user-jackie/Smart-Refrigerator/5.PCB File(made by jlc)/assets/image-20260305090433791.png

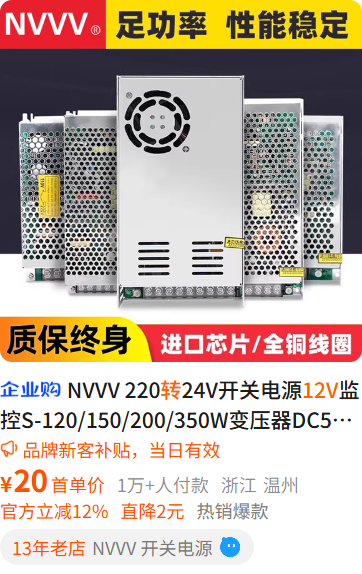
5.PCB File(made by jlc)/assets/image-20260305090433791.png
