user-jackie/Smart-Refrigerator/5.PCB File(made by jlc)/assets/image-20260305092447857.png

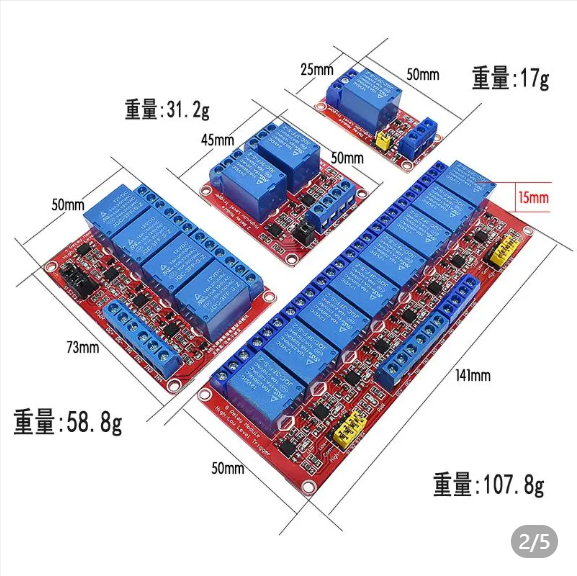
5.PCB File(made by jlc)/assets/image-20260305092447857.png
