user-jackie/Smart-Refrigerator/1.Shell(made by SW)/冰箱零件和装配体/继电器装配体.SLDASM

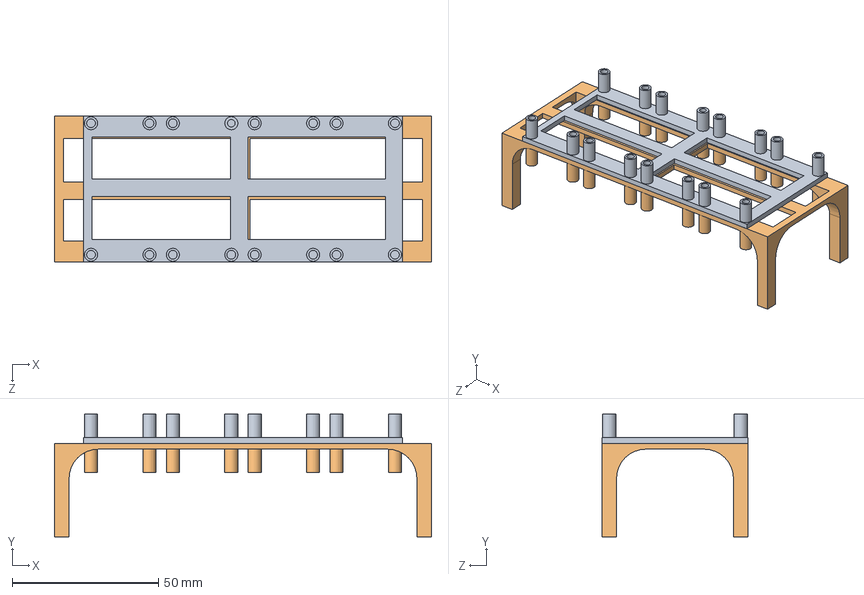
[picture p23: CAD file, 2026-03-05]
1.Shell(made by SW)/冰箱零件和装配体/继电器装配体.SLDASM
129.0 x 42.0 x 50.0 mm
继电器壳2
继电器壳
