user-jackie/Smart-Refrigerator/1.Shell(made by SW)/冰箱零件和装配体/装配体.SLDASM

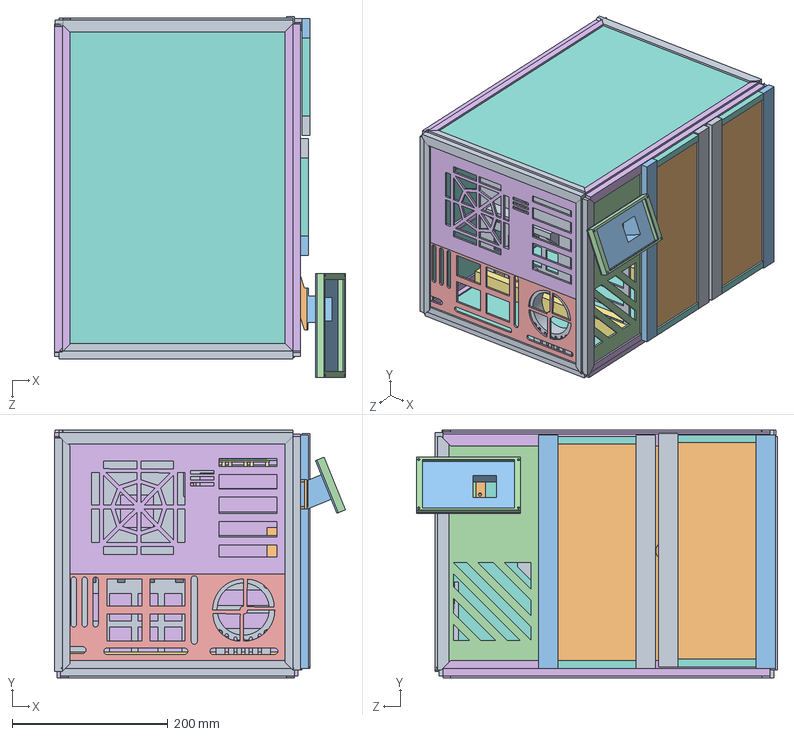
[picture p24: CAD file, 2026-03-05]
1.Shell(made by SW)/冰箱零件和装配体/装配体.SLDASM
373.7 x 318.0 x 464.2 mm
冰箱顶连接-短边 x 8
冰箱顶 x 3
冰箱侧1
冰箱顶连接-长边 x 4
冰箱侧2下
冰箱电源门
冰箱门 x 2
冰箱门亚克力 x 2
冰箱门磁吸侧 x 2
冰箱门包围 x 4
内胆卡槽 x 4
冰箱内冷热隔板
内胆顶 x 2
内胆热侧
内胆冷侧
内胆门吸
冰箱内电源隔板
继电器壳2
继电器壳
冰箱侧2上
PCB支撑
前屏幕罩
后屏幕罩
屏幕连接
空气净化外壳
