user-jackie/Smart-Refrigerator/1.Shell(made by SW)/冰箱零件和装配体/电源隔板装配体.SLDASM

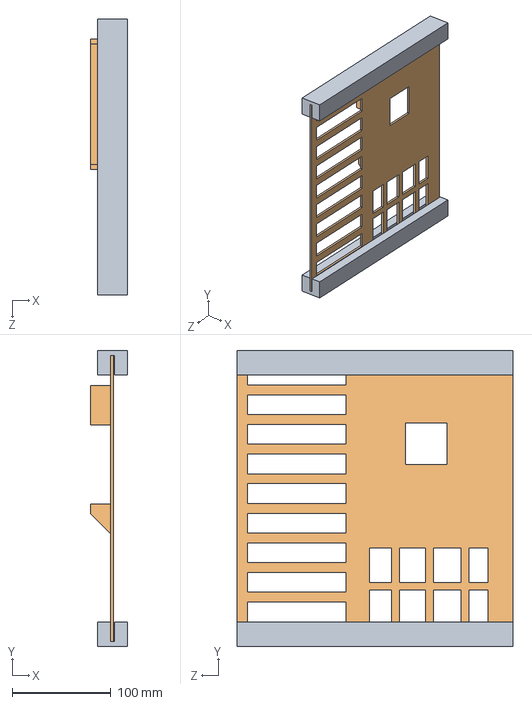
[picture p25: CAD file, 2026-03-05]
1.Shell(made by SW)/冰箱零件和装配体/电源隔板装配体.SLDASM
37.0 x 300.0 x 280.0 mm
冰箱内电源隔板
内胆卡槽 x 2
