user-jackie/Smart-Refrigerator/1.Shell(made by SW)/冰箱零件和装配体/屏幕装配体.SLDASM

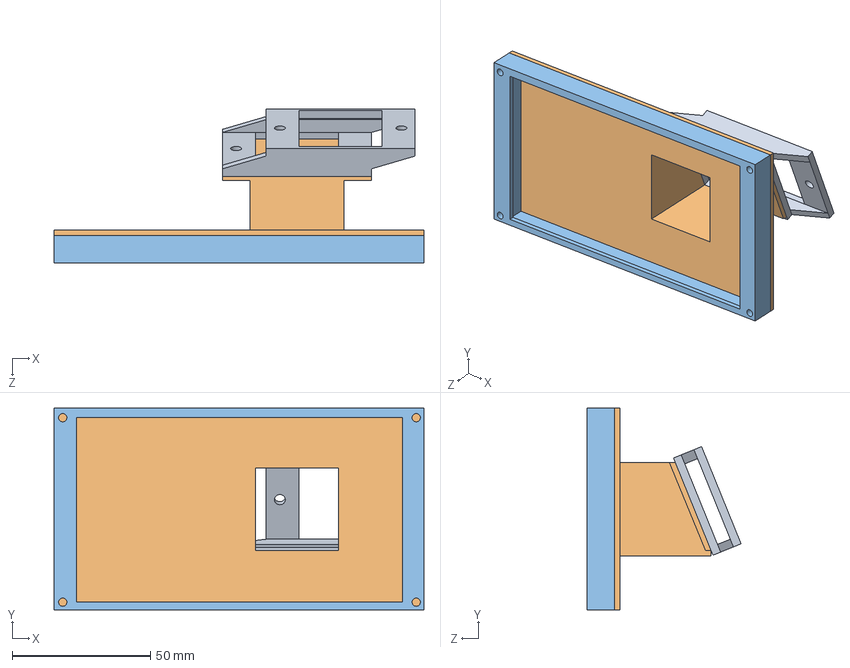
[picture p26: CAD file, 2026-03-05]
1.Shell(made by SW)/冰箱零件和装配体/屏幕装配体.SLDASM
134.0 x 73.0 x 55.9 mm
前屏幕罩
后屏幕罩
屏幕连接
