user-jackie/Smart-Refrigerator/1.Shell(made by SW)/打印文件/继电器壳2.STL

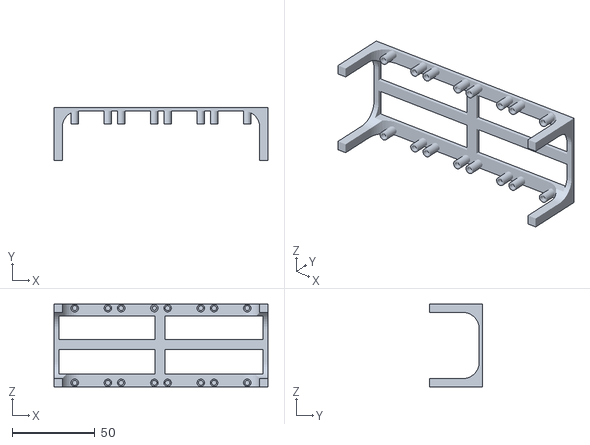
[picture p39: CAD file, 2026-03-05]
1.Shell(made by SW)/打印文件/继电器壳2.STL
129.0 x 32.0 x 50.0
