user-jackie/Smart-Refrigerator/1.Shell(made by SW)/冰箱零件和装配体/六角螺栓 M6x5.SLDPRT

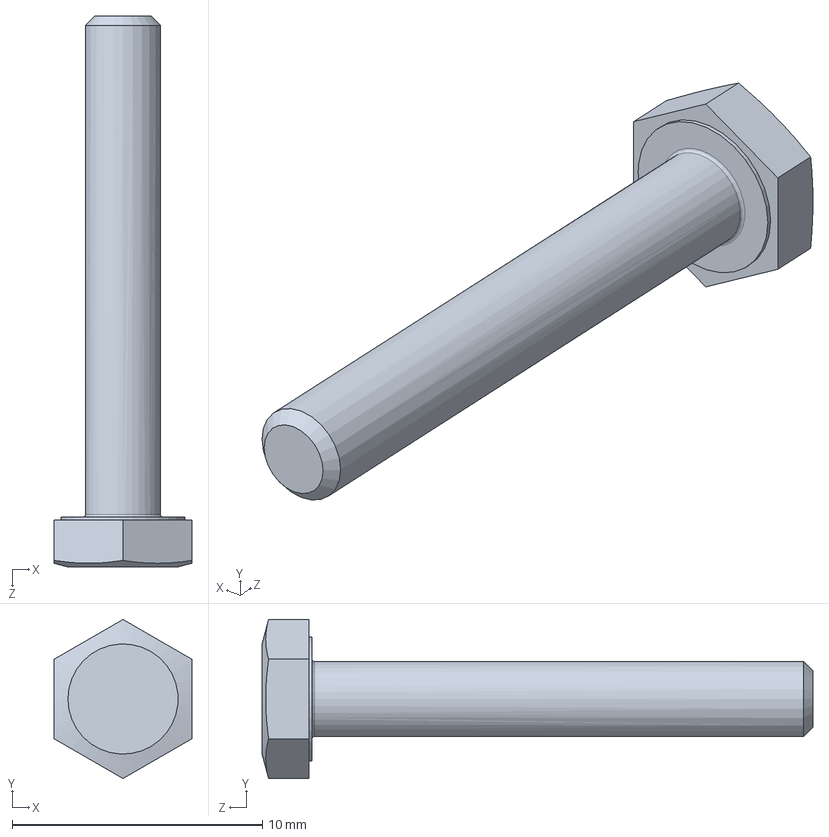
[picture p40: CAD file, 2026-03-05]
1.Shell(made by SW)/冰箱零件和装配体/六角螺栓 M6x5.SLDPRT
5.50 x 6.35 x 22.0 mm
