user-jackie/Smart-Refrigerator/1.Shell(made by SW)/打印文件/内胆热侧001.stl

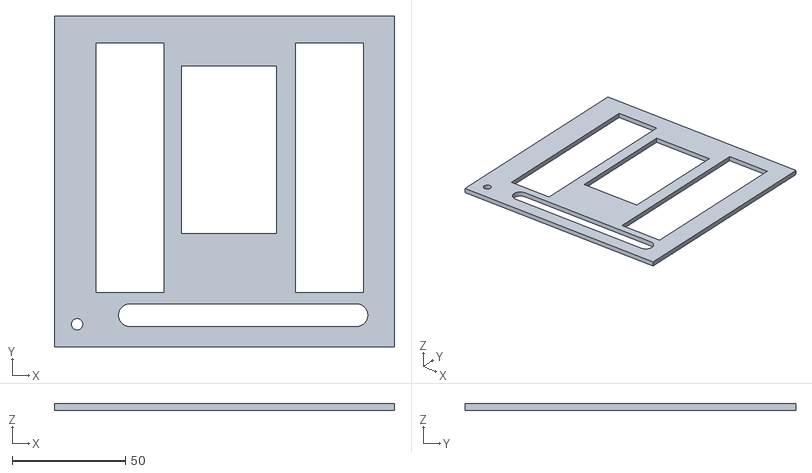
[picture p41: CAD file, 2026-03-05]
1.Shell(made by SW)/打印文件/内胆热侧001.stl
150.0 x 145.9 x 3.00
