user-jackie/Smart-Refrigerator/1.Shell(made by SW)/打印文件/冰箱门包围.STL

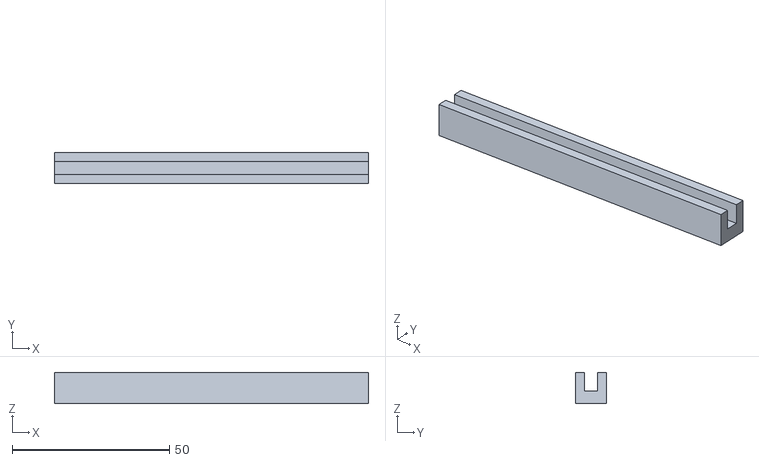
[picture p42: CAD file, 2026-03-05]
1.Shell(made by SW)/打印文件/冰箱门包围.STL
100.0 x 10.0 x 10.0
