user-jackie/Smart-Refrigerator/1.Shell(made by SW)/冰箱零件和装配体/冰箱门连接.SLDPRT

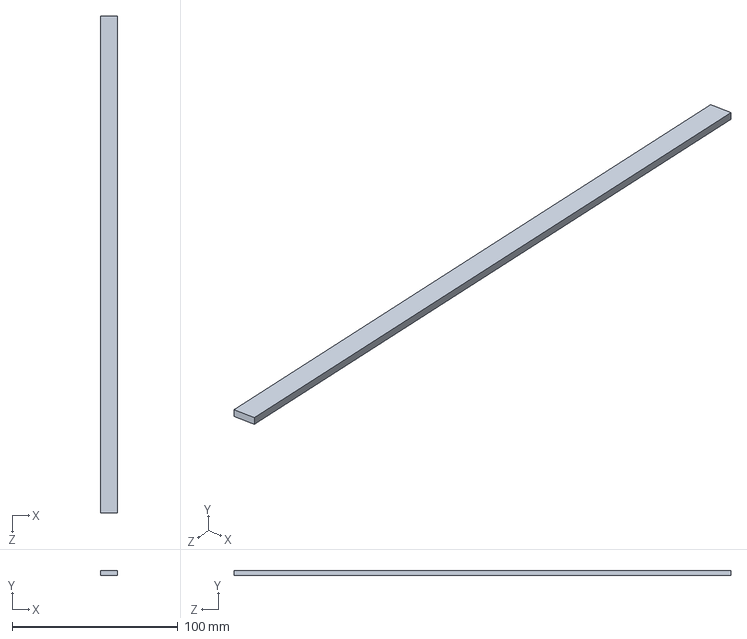
[picture p43: CAD file, 2026-03-05]
1.Shell(made by SW)/冰箱零件和装配体/冰箱门连接.SLDPRT
10.0 x 3.00 x 300.0 mm
