user-jackie/Smart-Refrigerator/1.Shell(made by SW)/打印文件/前屏幕罩.STL

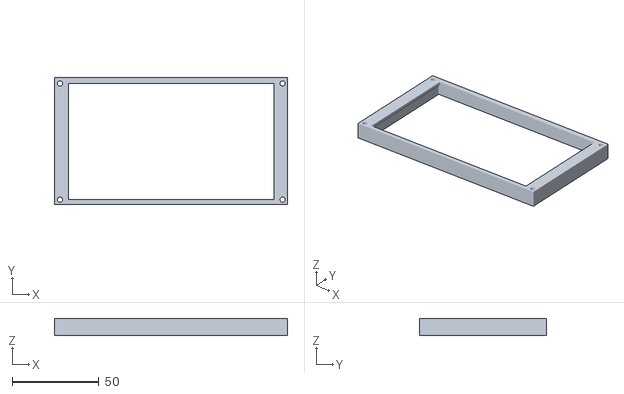
[picture p44: CAD file, 2026-03-05]
1.Shell(made by SW)/打印文件/前屏幕罩.STL
134.0 x 73.0 x 10.0
