user-jackie/Smart-Refrigerator/1.Shell(made by SW)/冰箱零件和装配体/冰箱.SLDPRT

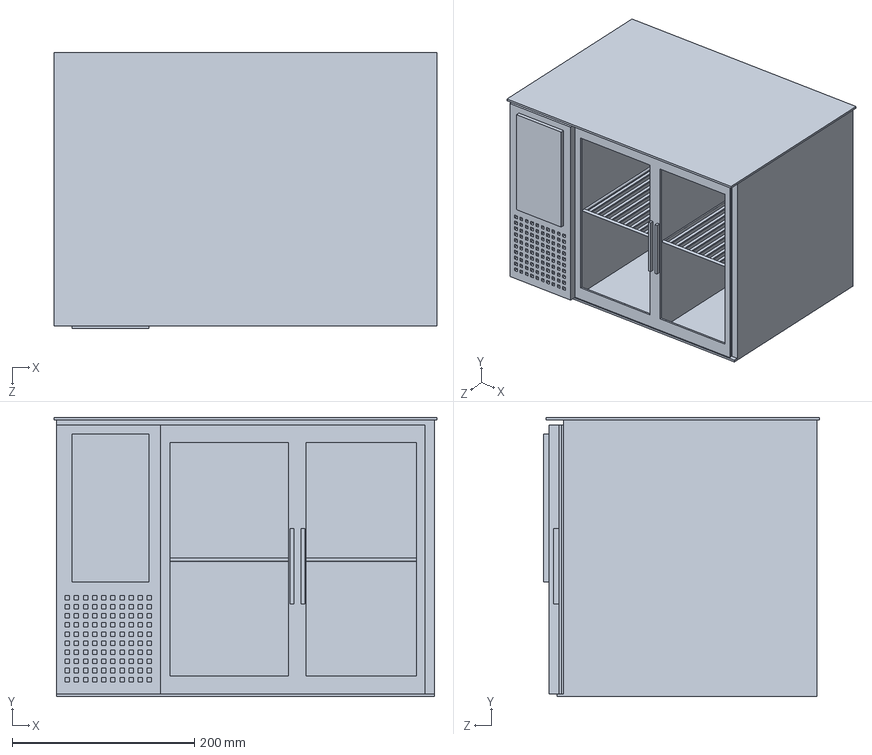
[picture p45: CAD file, 2026-03-05]
1.Shell(made by SW)/冰箱零件和装配体/冰箱.SLDPRT
420.0 x 306.0 x 303.0 mm
