user-jackie/Smart-Refrigerator/1.Shell(made by SW)/打印文件/冰箱电源门001.stl

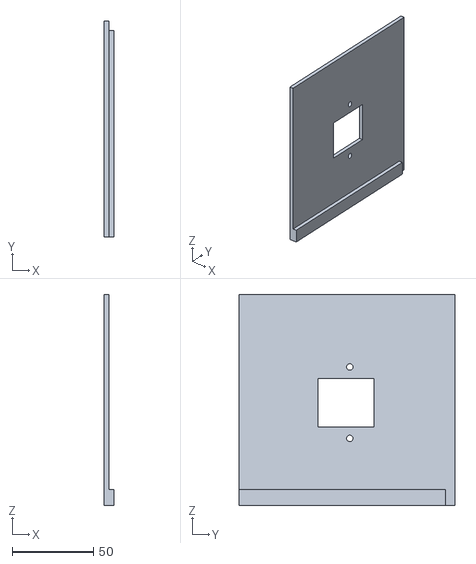
[picture p46: CAD file, 2026-03-05]
1.Shell(made by SW)/打印文件/冰箱电源门001.stl
6.00 x 133.1 x 130.0
