user-jackie/Smart-Refrigerator/1.Shell(made by SW)/打印文件/空气净化外壳.STL

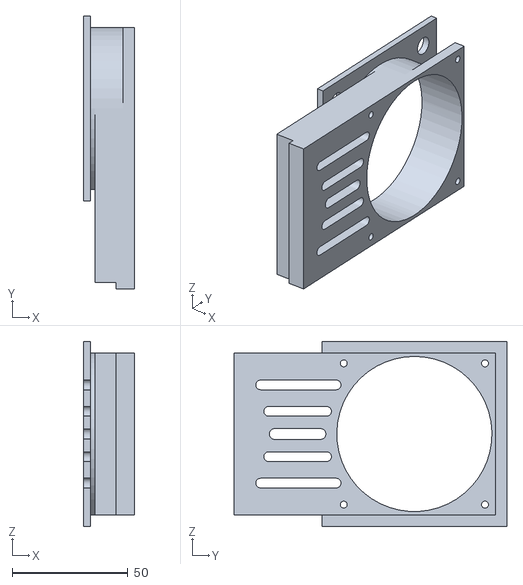
[picture p48: CAD file, 2026-03-05]
1.Shell(made by SW)/打印文件/空气净化外壳.STL
22.0 x 117.9 x 80.0
