user-jackie/Smart-Refrigerator/1.Shell(made by SW)/冰箱零件和装配体/侧连接.SLDPRT

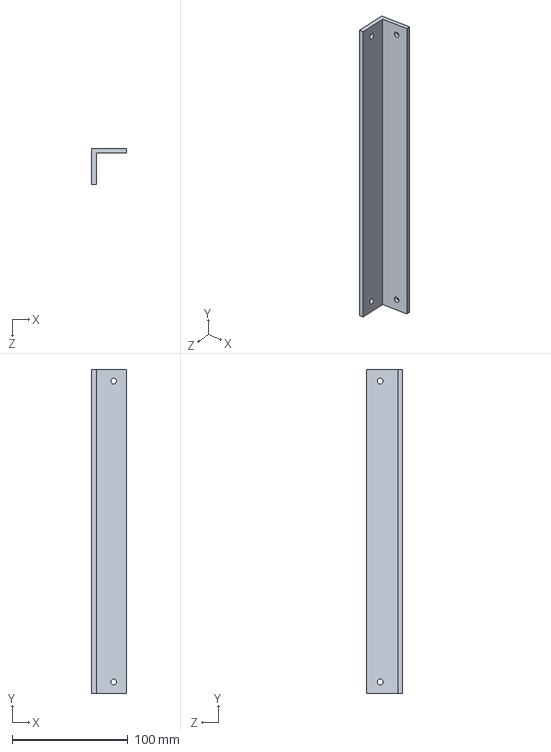
[picture p49: CAD file, 2026-03-05]
1.Shell(made by SW)/冰箱零件和装配体/侧连接.SLDPRT
30.0 x 280.0 x 30.7 mm
