user-jackie/Smart-Refrigerator/1.Shell(made by SW)/打印文件/冰箱内电源隔板004.stl

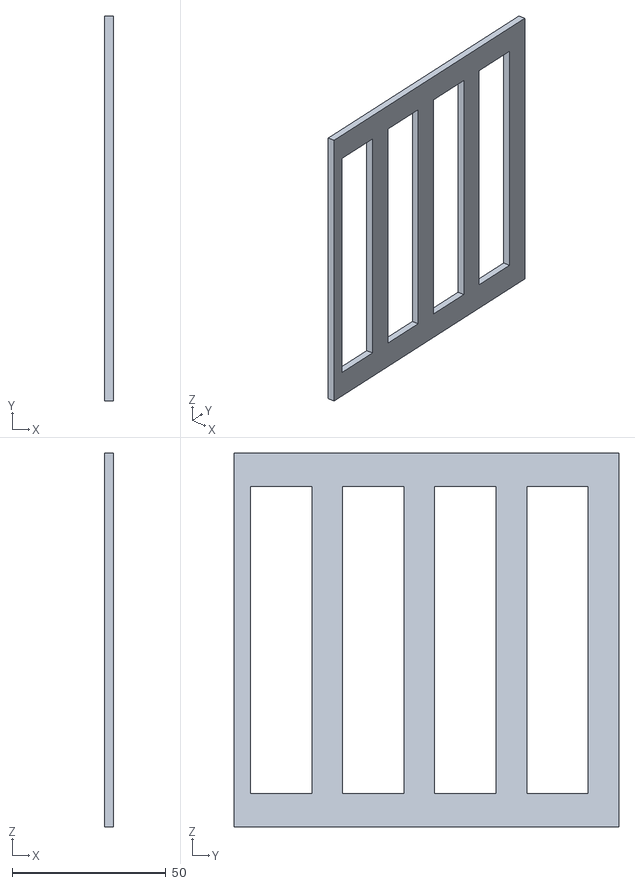
[picture p50: CAD file, 2026-03-05]
1.Shell(made by SW)/打印文件/冰箱内电源隔板004.stl
3.00 x 125.3 x 121.8
