user-jackie/Smart-Refrigerator/1.Shell(made by SW)/打印文件/冰箱侧2下.STL

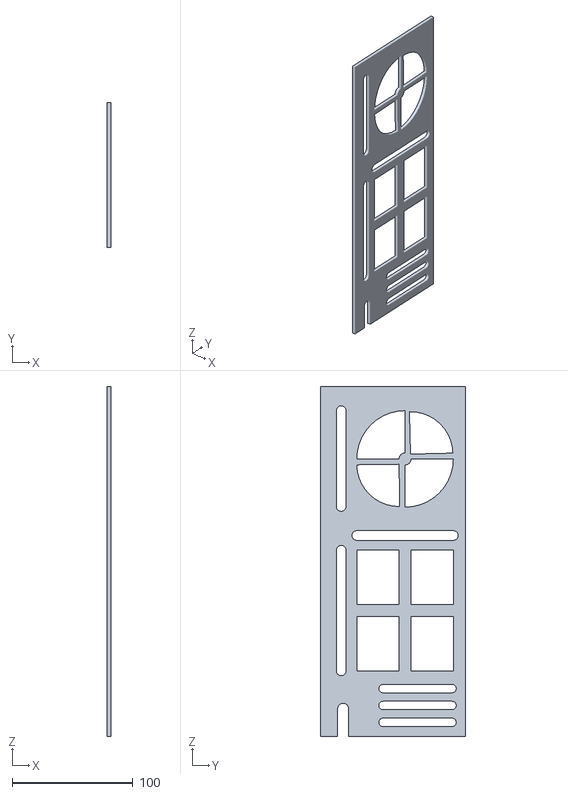
[picture p51: CAD file, 2026-03-05]
1.Shell(made by SW)/打印文件/冰箱侧2下.STL
3.00 x 120.0 x 290.0
