user-jackie/Smart-Refrigerator/1.Shell(made by SW)/打印文件/内胆卡槽.STL

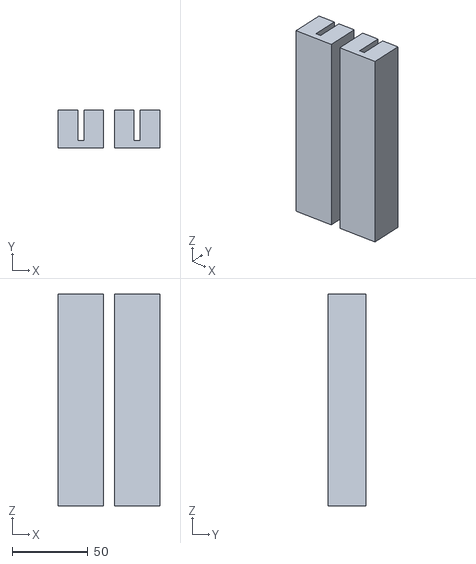
[picture p53: CAD file, 2026-03-05]
1.Shell(made by SW)/打印文件/内胆卡槽.STL
67.3 x 25.0 x 140.0
