user-jackie/Smart-Refrigerator/1.Shell(made by SW)/打印文件/内胆冷侧002.stl

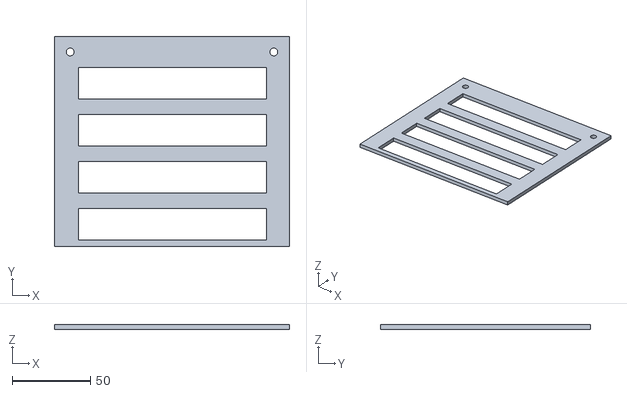
[picture p54: CAD file, 2026-03-05]
1.Shell(made by SW)/打印文件/内胆冷侧002.stl
150.0 x 134.3 x 3.00
