user-jackie/Smart-Refrigerator/1.Shell(made by SW)/冰箱零件和装配体/冰箱门.SLDPRT

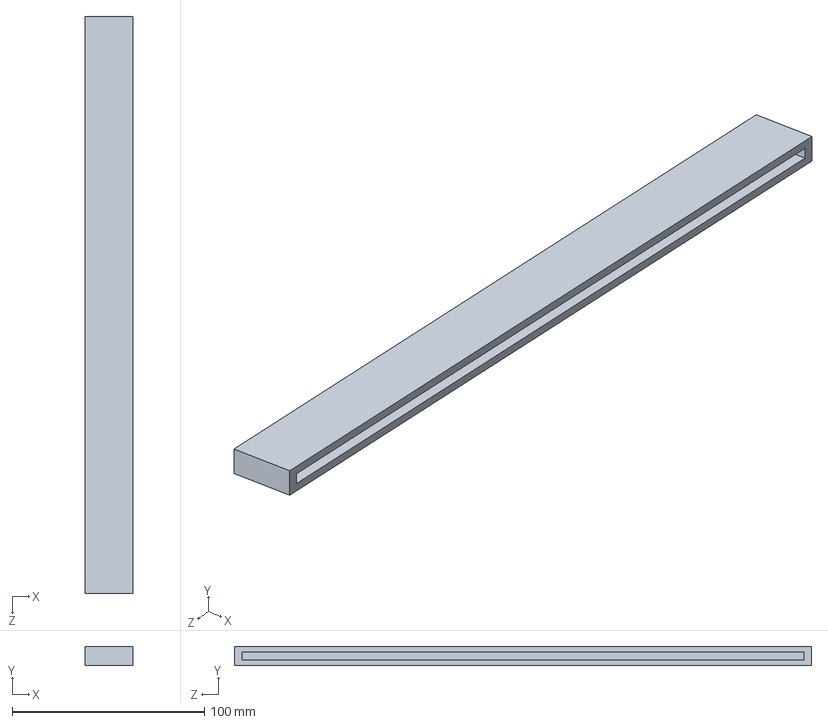
[picture p55: CAD file, 2026-03-05]
1.Shell(made by SW)/冰箱零件和装配体/冰箱门.SLDPRT
25.0 x 10.0 x 300.0 mm
