user-jackie/Smart-Refrigerator/1.Shell(made by SW)/打印文件/冰箱顶连接-短边.stl

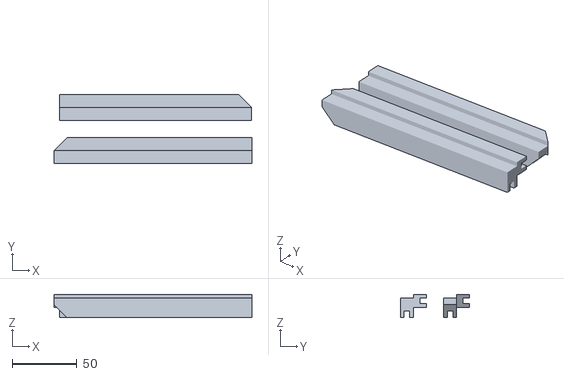
[picture p58: CAD file, 2026-03-05]
1.Shell(made by SW)/打印文件/冰箱顶连接-短边.stl
152.3 x 53.3 x 18.0
