user-jackie/Smart-Refrigerator/1.Shell(made by SW)/打印文件/冰箱内电源隔板001.stl

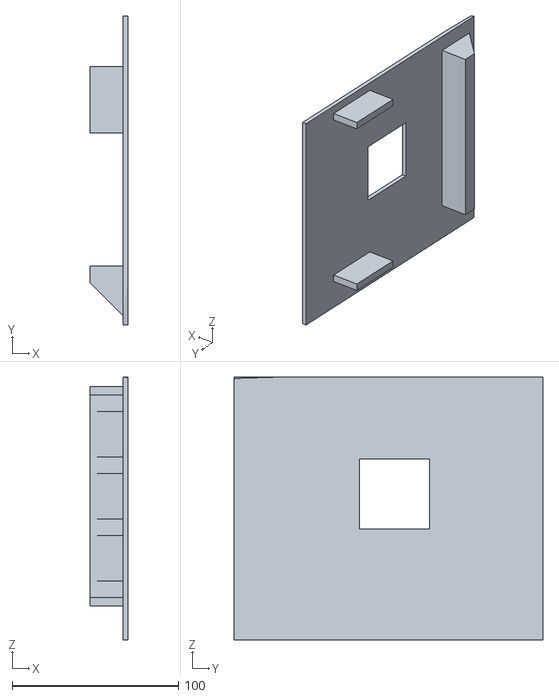
[picture p59: CAD file, 2026-03-05]
1.Shell(made by SW)/打印文件/冰箱内电源隔板001.stl
23.0 x 185.8 x 158.2
