user-jackie/Smart-Refrigerator/1.Shell(made by SW)/冰箱零件和装配体/PCB支撑.SLDPRT

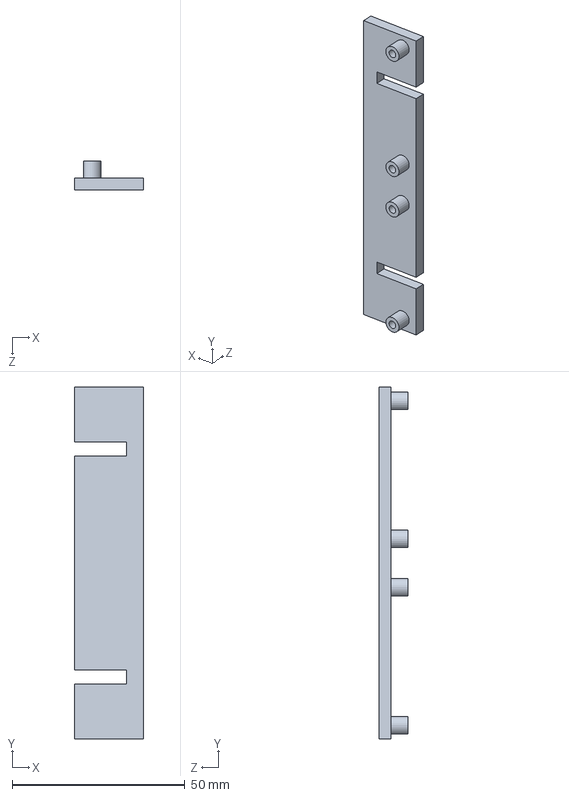
[picture p60: CAD file, 2026-03-05]
1.Shell(made by SW)/冰箱零件和装配体/PCB支撑.SLDPRT
20.0 x 102.0 x 8.50 mm
