user-jackie/Smart-Refrigerator/1.Shell(made by SW)/打印文件/杜邦线理线器.stl

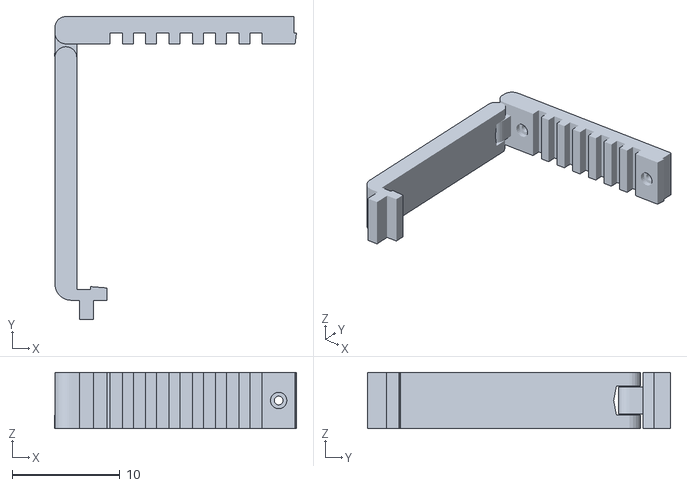
[picture p61: CAD file, 2026-03-05]
1.Shell(made by SW)/打印文件/杜邦线理线器.stl
22.4 x 28.1 x 5.24
