user-jackie/Smart-Refrigerator/1.Shell(made by SW)/打印文件/内胆顶.STL

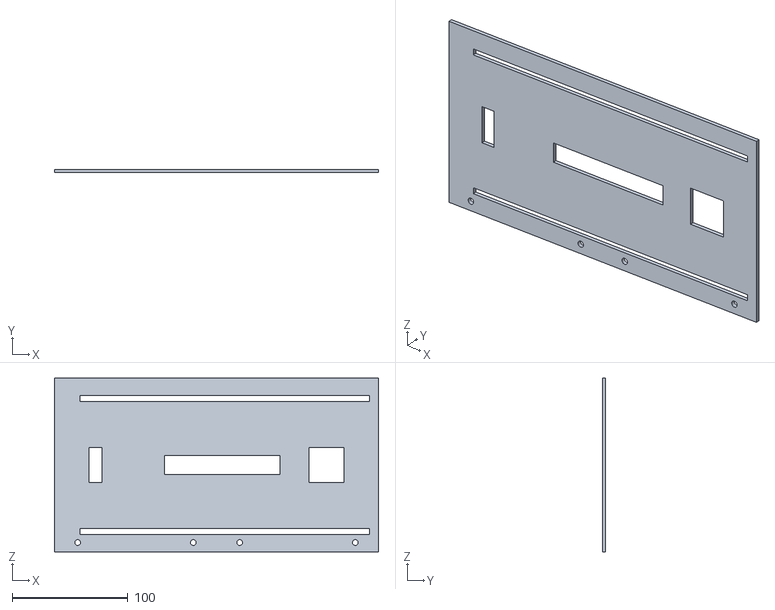
[picture p62: CAD file, 2026-03-05]
1.Shell(made by SW)/打印文件/内胆顶.STL
280.0 x 3.00 x 150.0
