user-jackie/Smart-Refrigerator/1.Shell(made by SW)/冰箱零件和装配体/冰箱电源门.SLDPRT

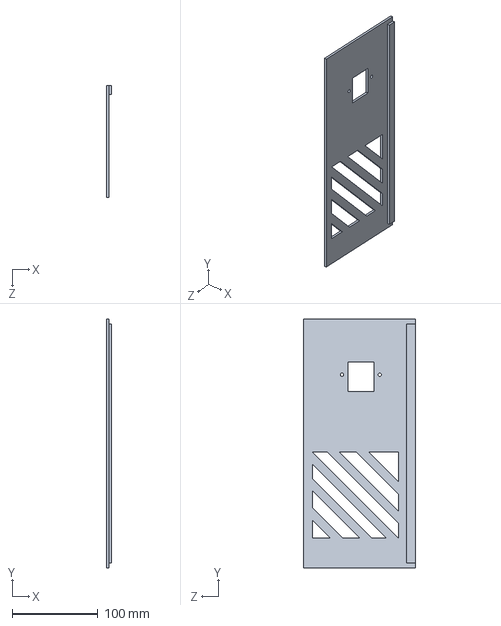
[picture p63: CAD file, 2026-03-05]
1.Shell(made by SW)/冰箱零件和装配体/冰箱电源门.SLDPRT
6.00 x 290.0 x 130.0 mm
