user-jackie/Smart-Refrigerator/1.Shell(made by SW)/打印文件/内胆顶001.stl

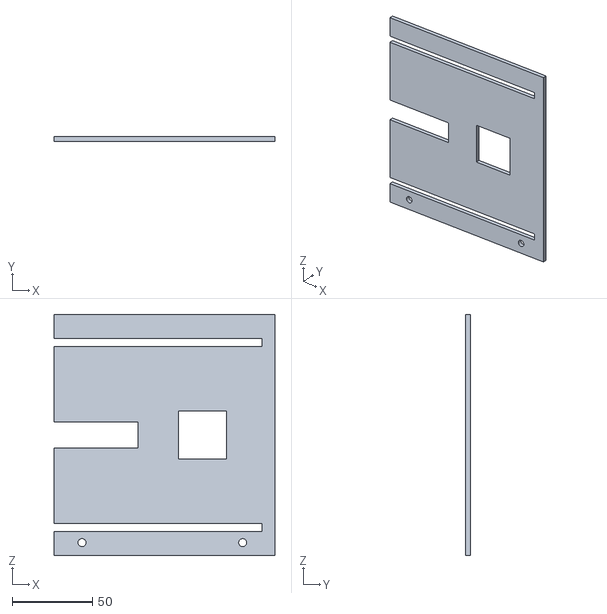
[picture p64: CAD file, 2026-03-05]
1.Shell(made by SW)/打印文件/内胆顶001.stl
137.3 x 3.00 x 150.0
