user-jackie/Smart-Refrigerator/1.Shell(made by SW)/冰箱零件和装配体/内胆门吸.SLDPRT

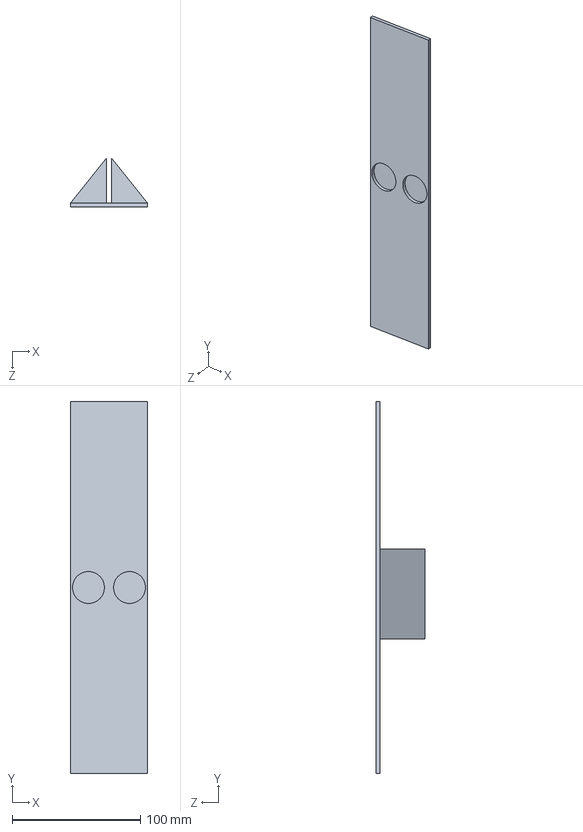
[picture p65: CAD file, 2026-03-05]
1.Shell(made by SW)/冰箱零件和装配体/内胆门吸.SLDPRT
60.0 x 290.0 x 38.0 mm
