user-jackie/Smart-Refrigerator/1.Shell(made by SW)/打印文件/冰箱内电源隔板002.stl

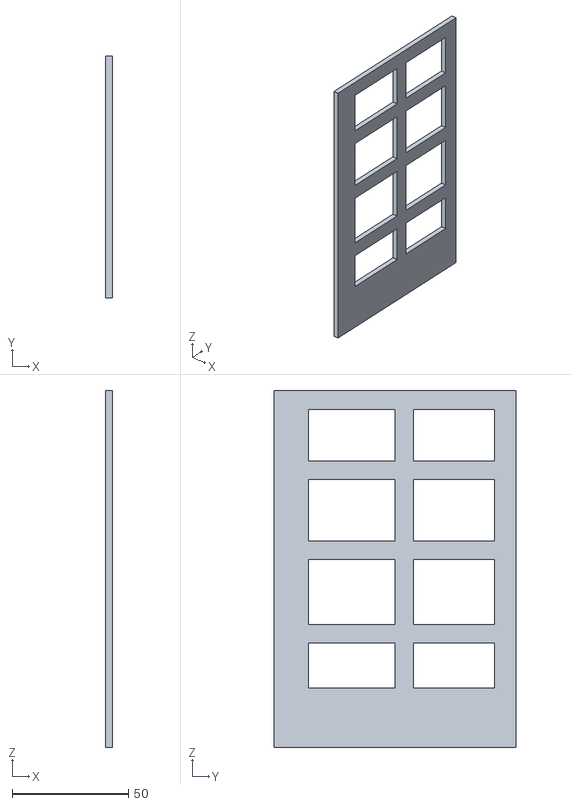
[picture p66: CAD file, 2026-03-05]
1.Shell(made by SW)/打印文件/冰箱内电源隔板002.stl
3.00 x 104.2 x 153.6
