user-jackie/Smart-Refrigerator/1.Shell(made by SW)/打印文件/冰箱内电源隔板003.stl

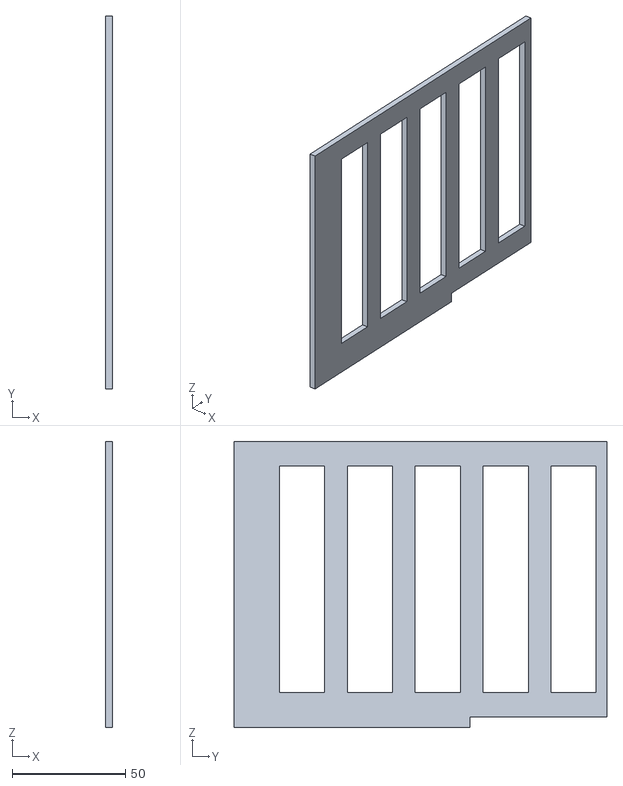
[picture p67: CAD file, 2026-03-05]
1.Shell(made by SW)/打印文件/冰箱内电源隔板003.stl
3.00 x 164.7 x 126.4
