user-jackie/Smart-Refrigerator/1.Shell(made by SW)/冰箱零件和装配体/冰箱门亚克力.SLDPRT

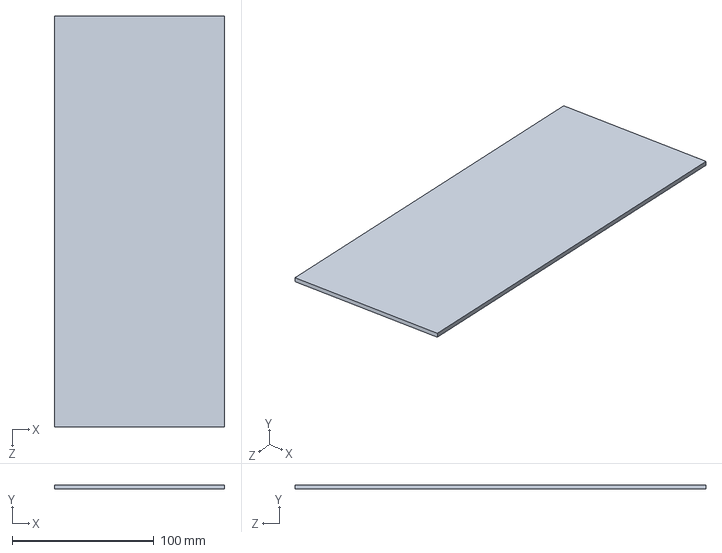
[picture p68: CAD file, 2026-03-05]
1.Shell(made by SW)/冰箱零件和装配体/冰箱门亚克力.SLDPRT
120.0 x 3.00 x 290.0 mm
