user-jackie/Smart-Refrigerator/1.Shell(made by SW)/打印文件/冰箱侧2上001.stl

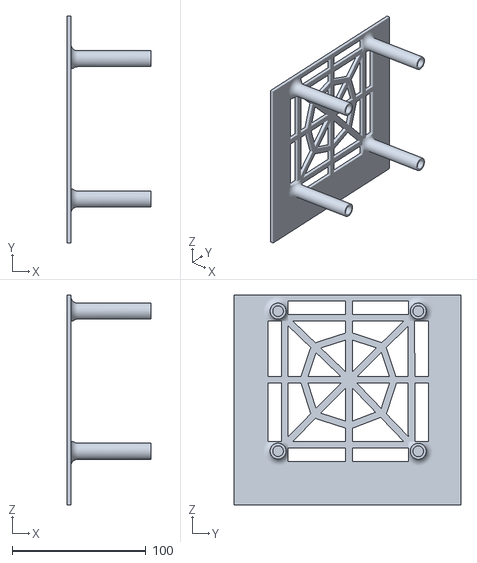
[picture p69: CAD file, 2026-03-05]
1.Shell(made by SW)/打印文件/冰箱侧2上001.stl
63.0 x 170.0 x 157.3
