user-jackie/Smart-Refrigerator/1.Shell(made by SW)/冰箱零件和装配体/冰箱顶连接-长边.SLDPRT

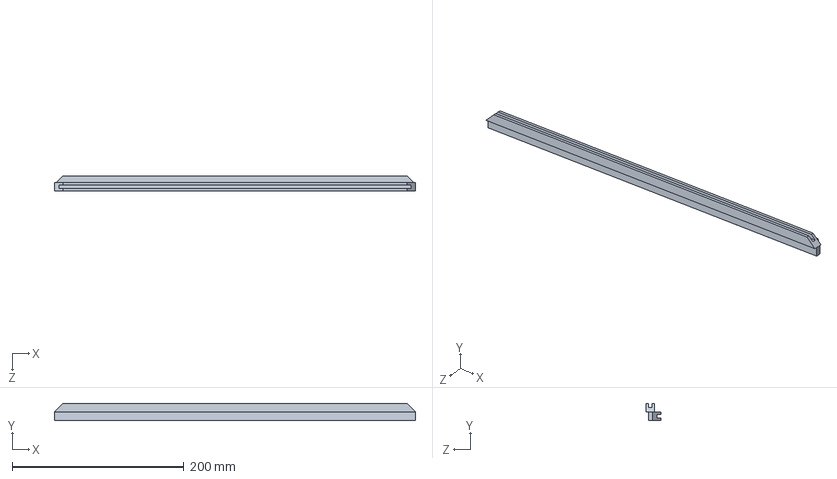
[picture p70: CAD file, 2026-03-05]
1.Shell(made by SW)/冰箱零件和装配体/冰箱顶连接-长边.SLDPRT
420.0 x 20.0 x 18.0 mm
