user-jackie/Smart-Refrigerator/1.Shell(made by SW)/冰箱零件和装配体/内胆卡槽.SLDPRT

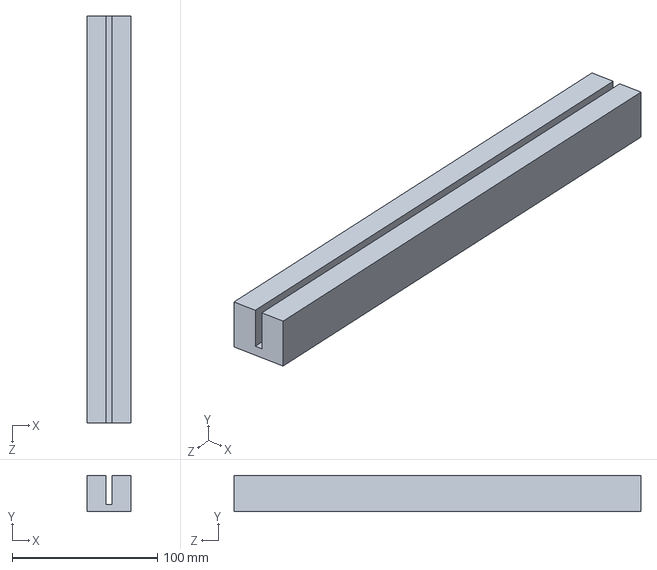
[picture p71: CAD file, 2026-03-05]
1.Shell(made by SW)/冰箱零件和装配体/内胆卡槽.SLDPRT
30.0 x 25.0 x 280.0 mm
