user-jackie/Smart-Refrigerator/1.Shell(made by SW)/打印文件/内胆顶002.stl

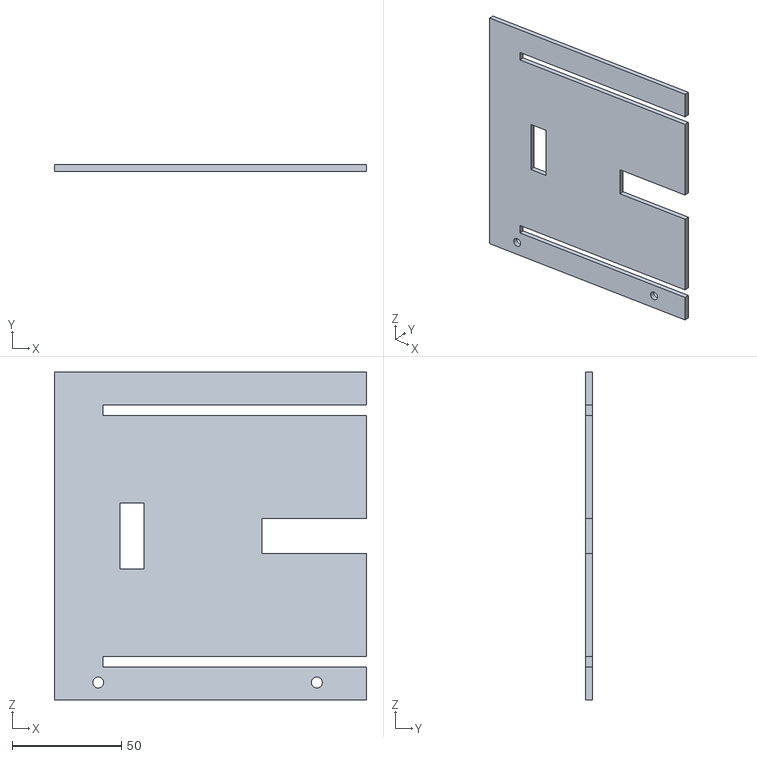
[picture p72: CAD file, 2026-03-05]
1.Shell(made by SW)/打印文件/内胆顶002.stl
142.7 x 3.00 x 150.0
