user-jackie/Smart-Refrigerator/1.Shell(made by SW)/冰箱零件和装配体/冰箱内电源隔板.SLDPRT

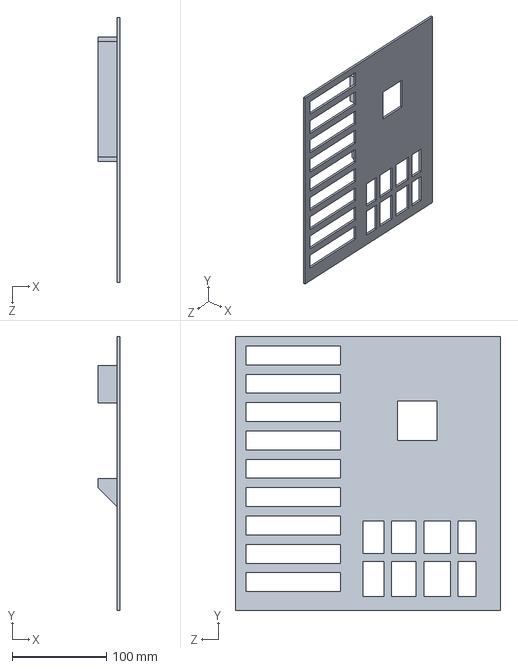
[picture p73: CAD file, 2026-03-05]
1.Shell(made by SW)/冰箱零件和装配体/冰箱内电源隔板.SLDPRT
23.0 x 290.0 x 280.0 mm
