user-jackie/Smart-Refrigerator/1.Shell(made by SW)/打印文件/冰箱顶连接-长边.stl

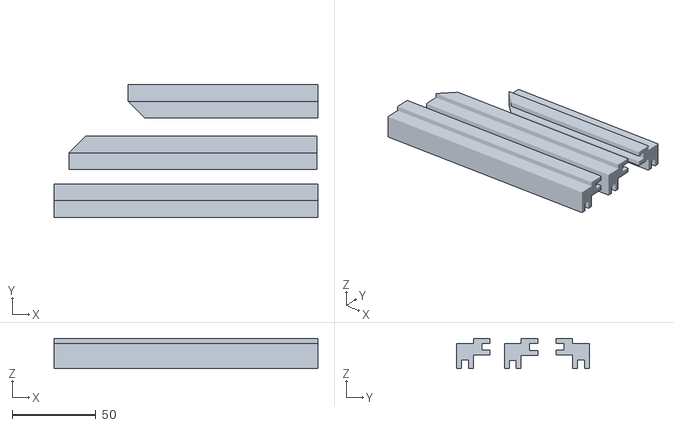
[picture p75: CAD file, 2026-03-05]
1.Shell(made by SW)/打印文件/冰箱顶连接-长边.stl
157.9 x 79.3 x 18.2
