user-jackie/Smart-Refrigerator/1.Shell(made by SW)/打印文件/冰箱侧2上002.stl

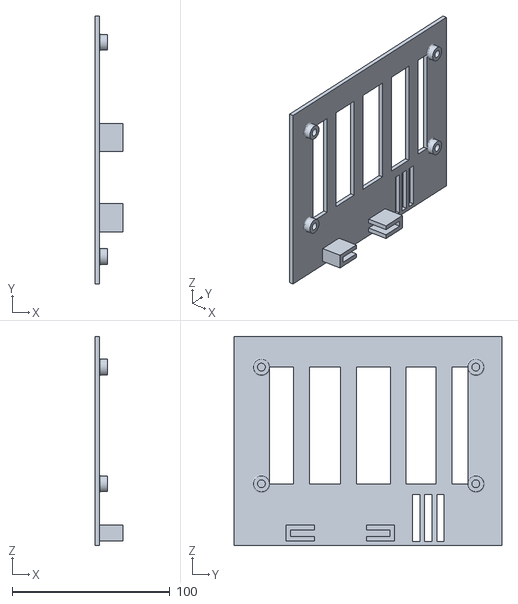
[picture p76: CAD file, 2026-03-05]
1.Shell(made by SW)/打印文件/冰箱侧2上002.stl
18.0 x 170.0 x 132.7
