user-jackie/Smart-Refrigerator/1.Shell(made by SW)/冰箱零件和装配体/门密封.SLDPRT

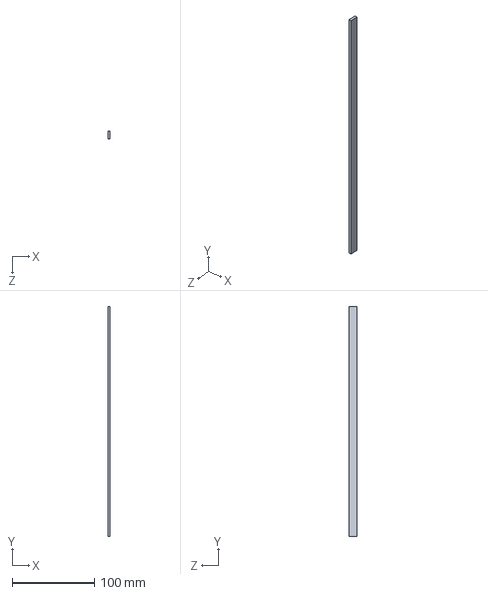
[picture p77: CAD file, 2026-03-05]
1.Shell(made by SW)/冰箱零件和装配体/门密封.SLDPRT
3.00 x 280.0 x 10.0 mm
