user-jackie/Smart-Refrigerator/1.Shell(made by SW)/打印文件/冰箱侧2下001.stl

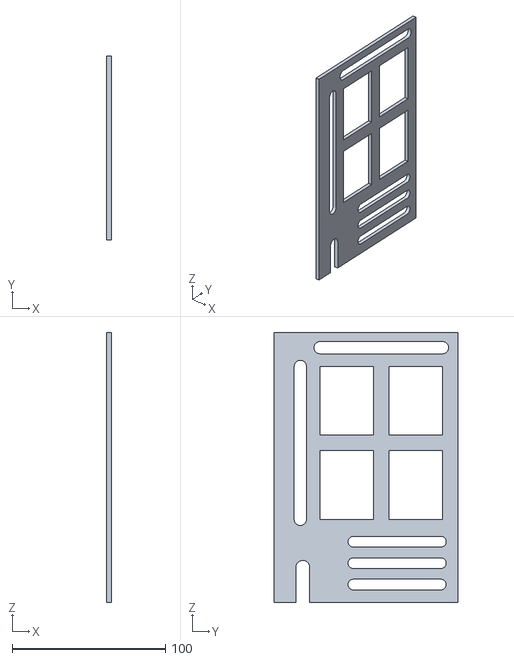
[picture p78: CAD file, 2026-03-05]
1.Shell(made by SW)/打印文件/冰箱侧2下001.stl
3.00 x 120.0 x 176.5
