user-jackie/Smart-Refrigerator/1.Shell(made by SW)/冰箱零件和装配体/Refri True TBB 24 48G S HC LD.SLDPRT

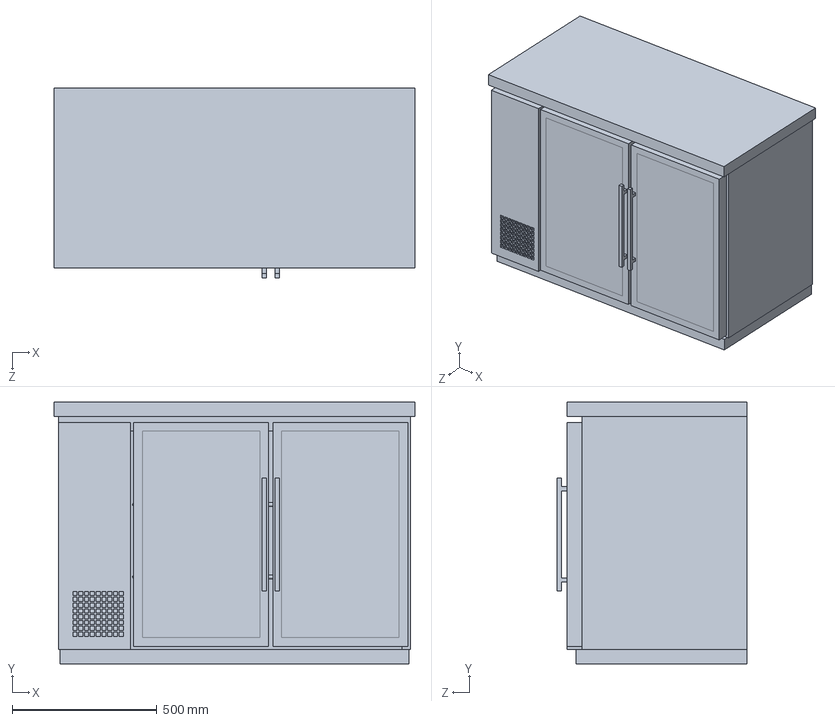
[picture p79: CAD file, 2026-03-05]
1.Shell(made by SW)/冰箱零件和装配体/Refri True TBB 24 48G S HC LD.SLDPRT
1247.0 x 905.0 x 656.0 mm
