user-jackie/Smart-Refrigerator/1.Shell(made by SW)/打印文件/内胆门吸.STL

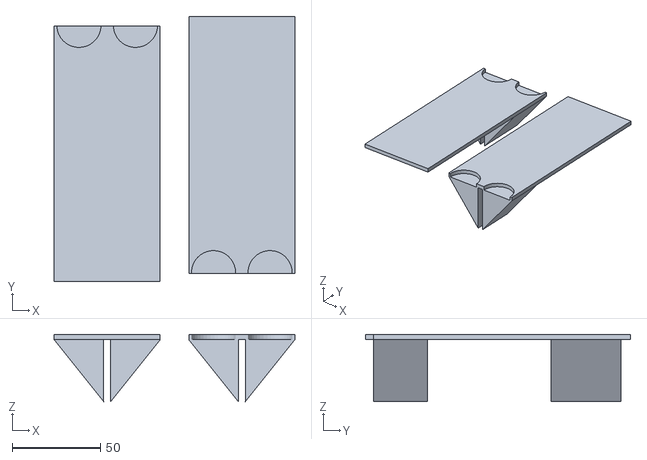
[picture p80: CAD file, 2026-03-05]
1.Shell(made by SW)/打印文件/内胆门吸.STL
136.2 x 150.0 x 38.0
