user-jackie/Smart-Refrigerator/1.Shell(made by SW)/冰箱零件和装配体/内胆热侧.SLDPRT

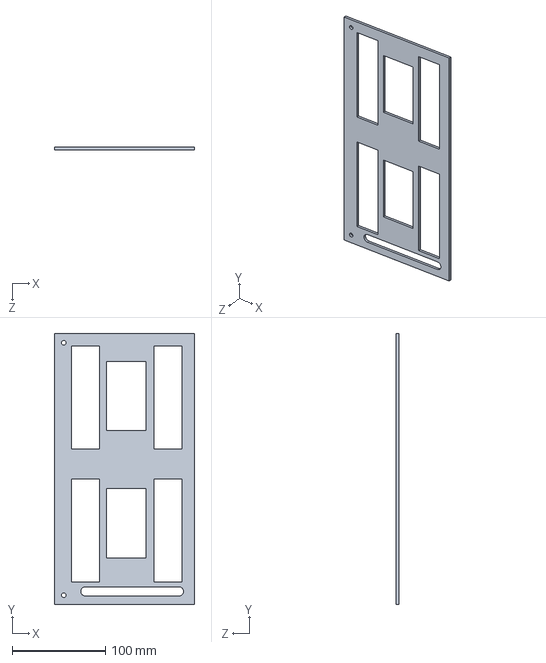
[picture p81: CAD file, 2026-03-05]
1.Shell(made by SW)/冰箱零件和装配体/内胆热侧.SLDPRT
150.0 x 290.0 x 3.00 mm
